smile5/MOMYX/Hardware/Valve/Valve VTT V2/BOISSEAU VALVE VTT V2.STL

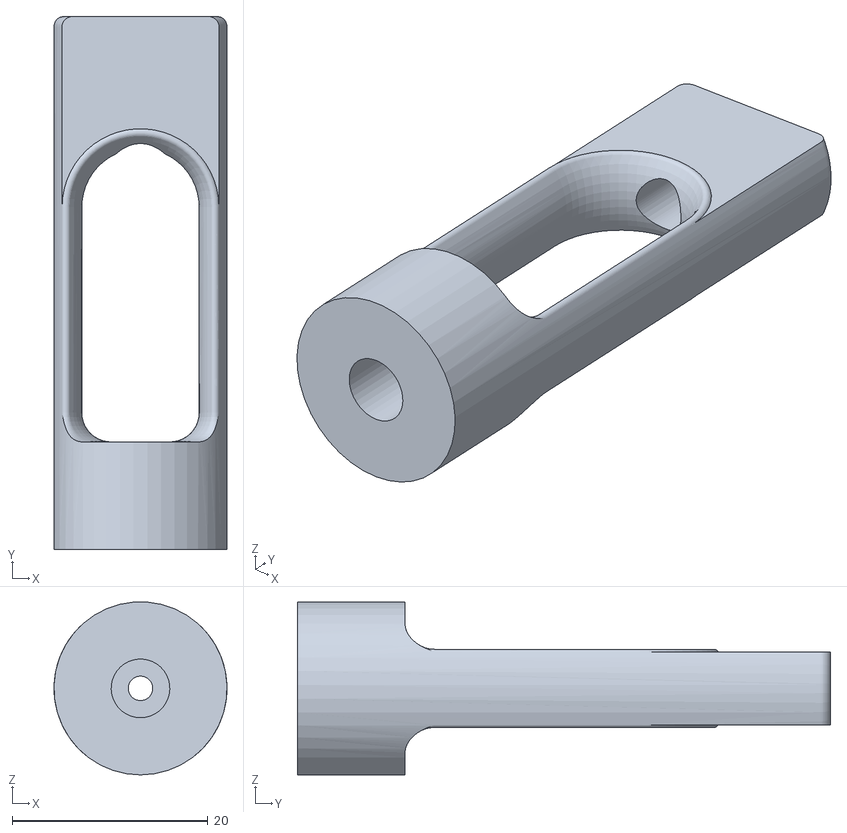
[picture p26: CAD file, 2020-05-29]
Hardware/Valve/Valve VTT V2/BOISSEAU VALVE VTT V2.STL
17.7 x 54.5 x 17.7
