smile5/MOMYX/Hardware/Venturi/Venturi V5.STL

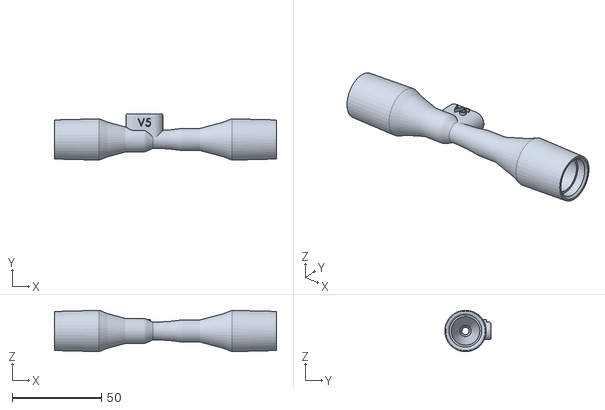
[picture p27: CAD file, 2020-05-15]
Hardware/Venturi/Venturi V5.STL
124.1 x 25.9 x 23.1
