smile5/MOMYX/Hardware/Turbines/COUVERCLE TURBINE V 3.5.DXF

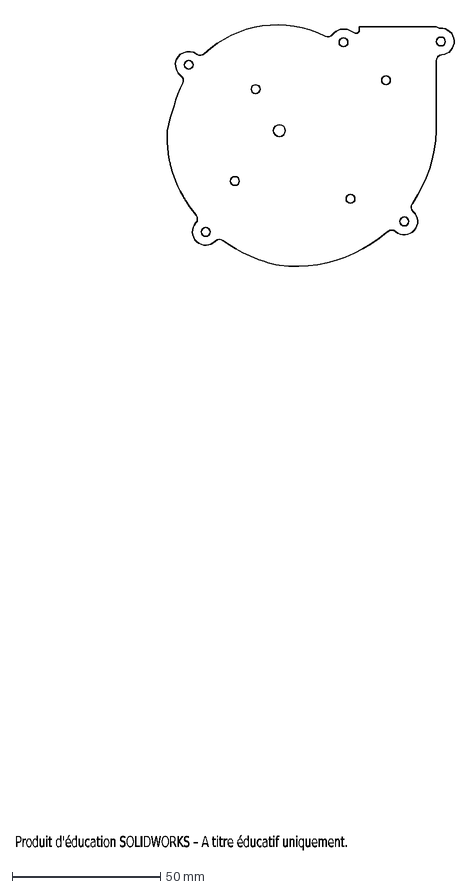
[picture p28: CAD file, 2020-06-02]
Hardware/Turbines/COUVERCLE TURBINE V 3.5.DXF
Produit d'éducation SOLIDWORKS – A titre éducatif uniquement.
