smile5/MOMYX/Hardware/Venturi/Nid abeille V2.STL

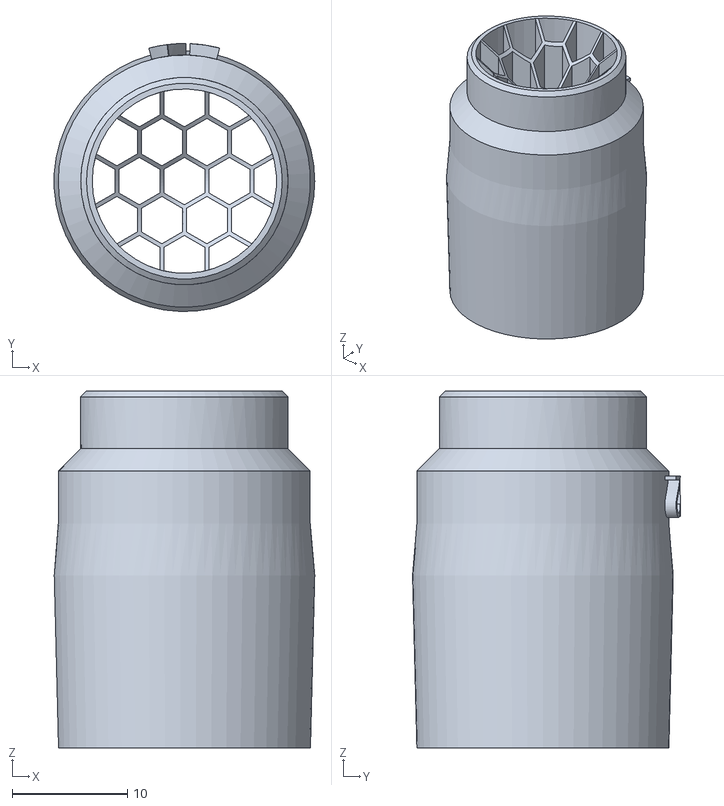
[picture p29: CAD file, 2020-05-15]
Hardware/Venturi/Nid abeille V2.STL
22.6 x 23.3 x 31.0
