smile5/MOMYX/Hardware/Turbines/SUPPORT TURBINE V 3.5.STL

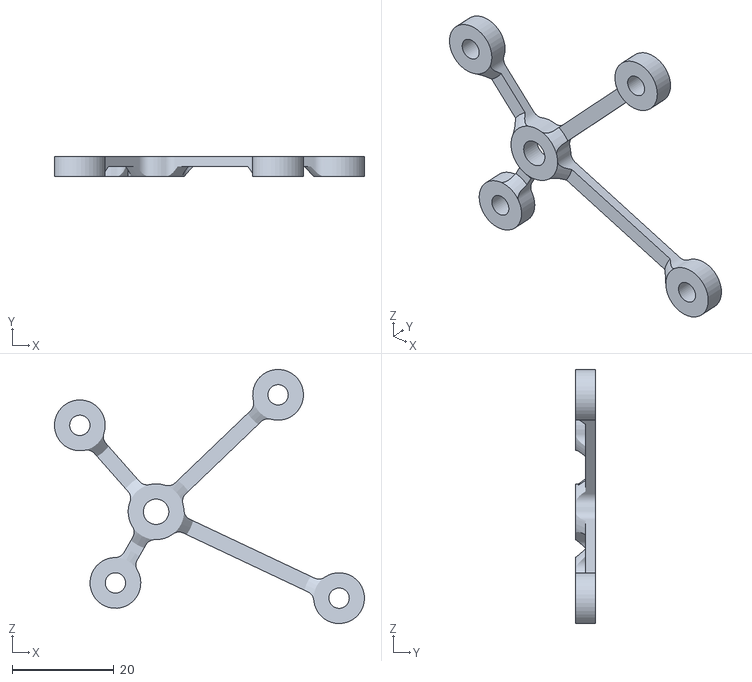
[picture p30: CAD file, 2020-06-02]
Hardware/Turbines/SUPPORT TURBINE V 3.5.STL
61.0 x 4.00 x 50.0
